jankae/battery-sim/pictures/IMG_2403.JPG

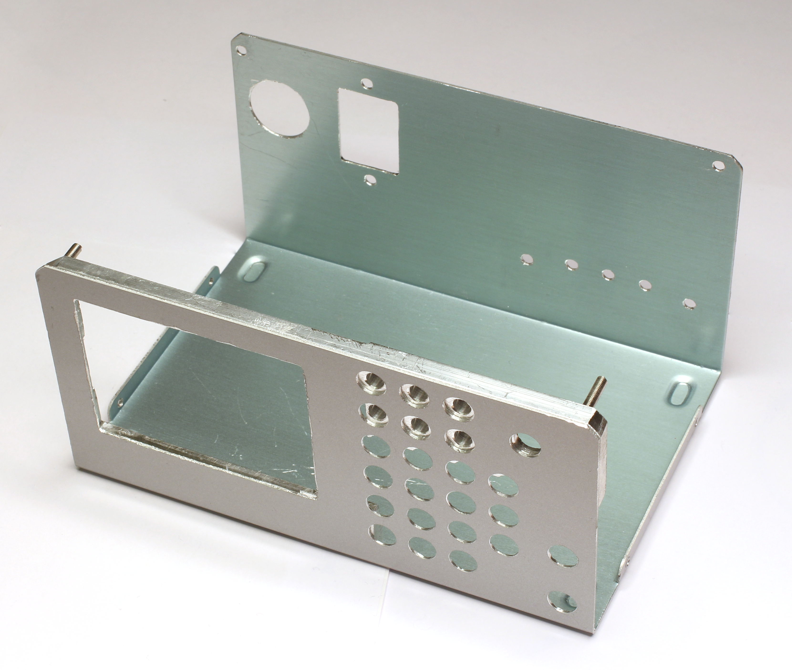
pictures/IMG_2403.JPG
