jankae/battery-sim/pictures/IMG_2404.JPG

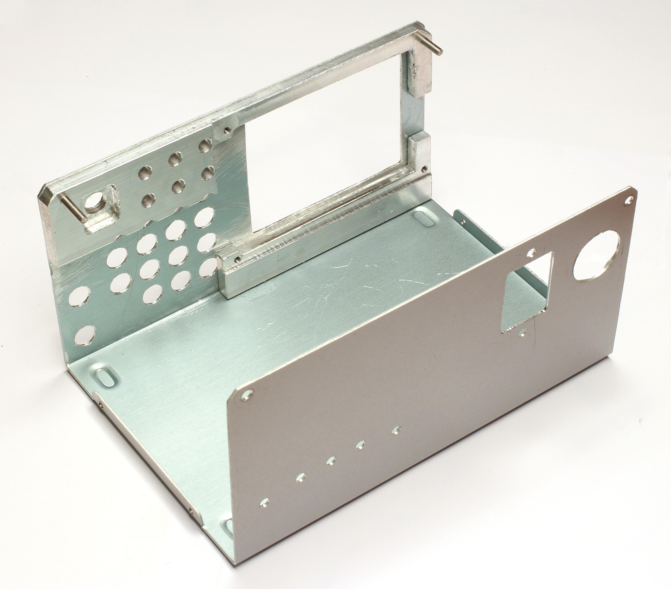
pictures/IMG_2404.JPG
