jankae/battery-sim/pictures/IMG_2405.JPG

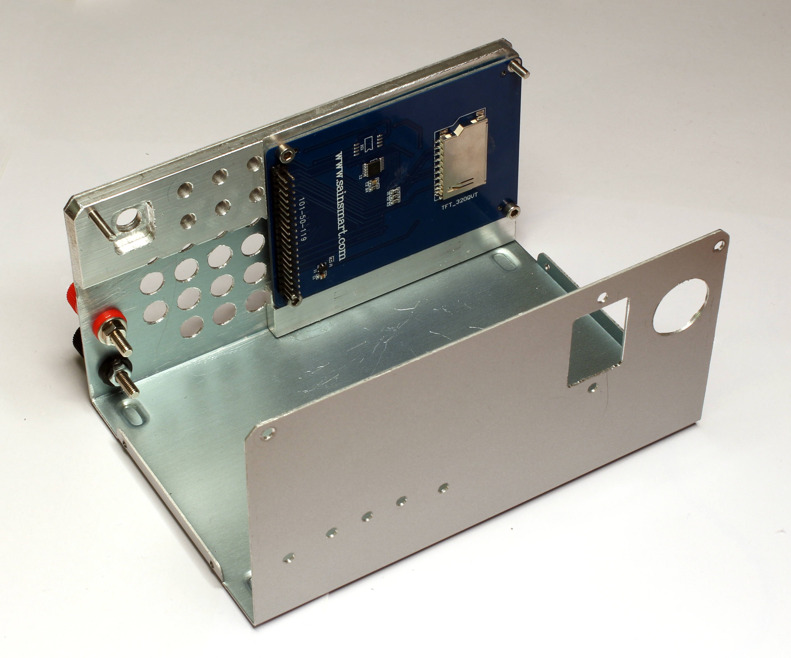
pictures/IMG_2405.JPG
