jankae/battery-sim/pictures/IMG_2406.JPG

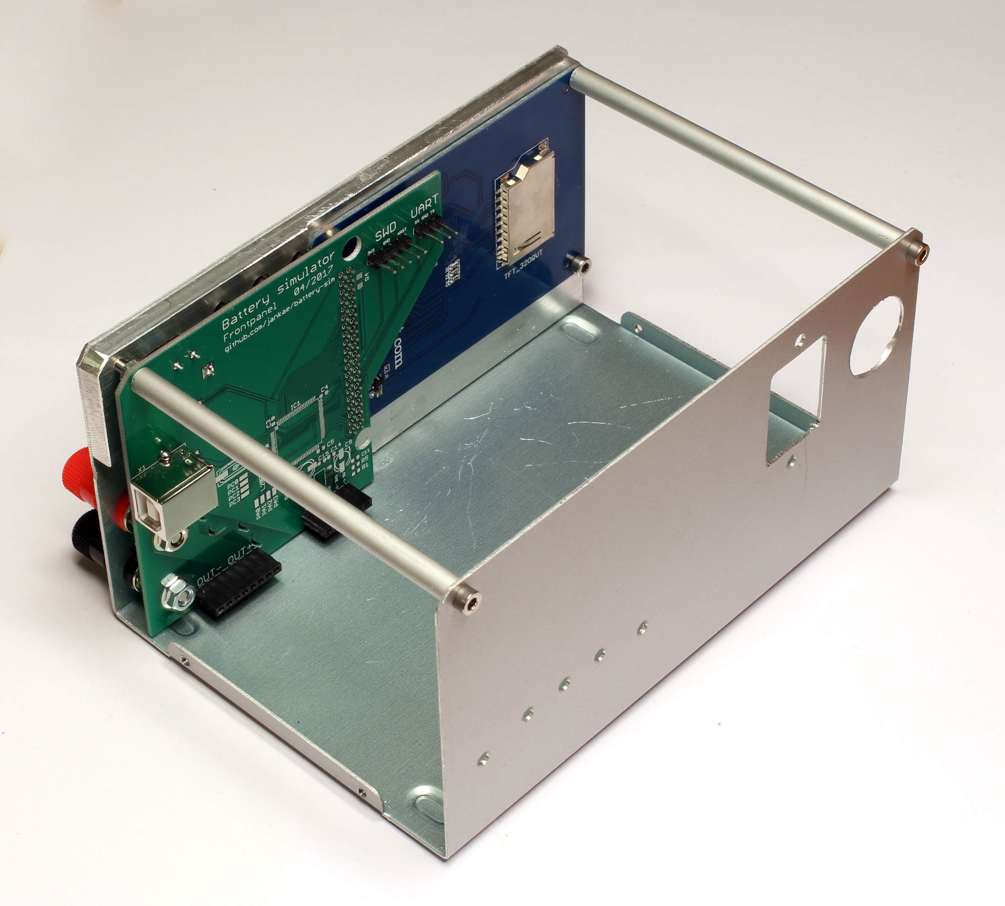
pictures/IMG_2406.JPG
