jankae/battery-sim/pictures/IMG_2407.JPG

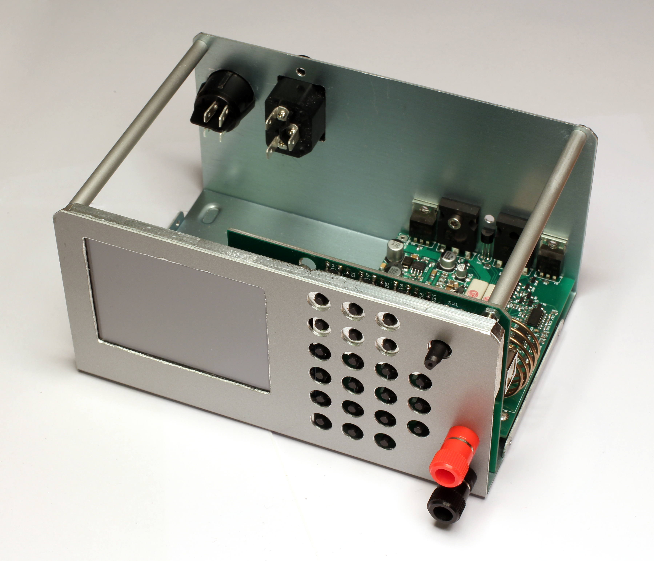
pictures/IMG_2407.JPG
