jankae/battery-sim/pictures/IMG_4996.JPG

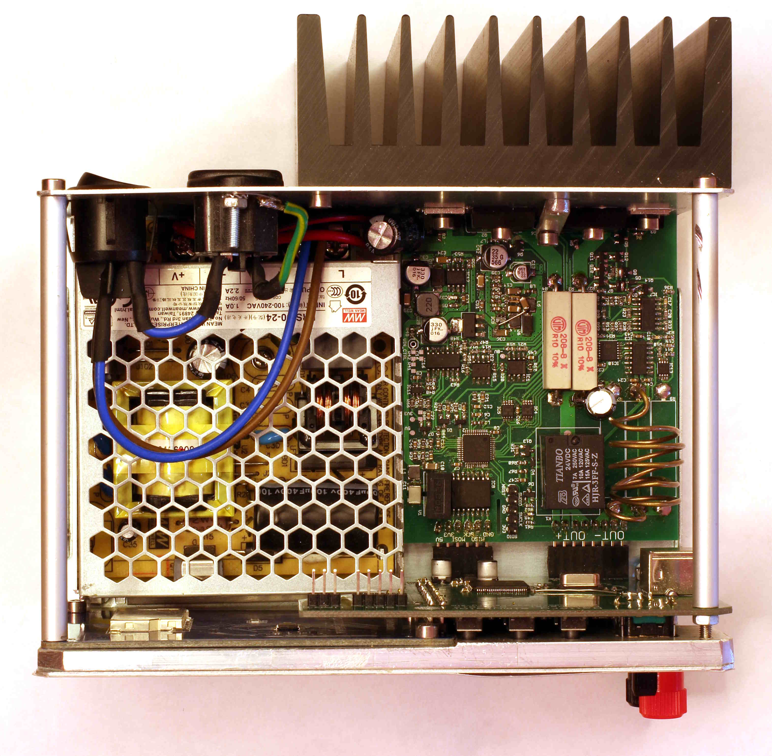
pictures/IMG_4996.JPG
