jankae/battery-sim/software/batsim/Abstraction/display.h

#ifndef DISPLAY_H_
#define DISPLAY_H_

#include "gpio.h"
#include "font.h"
#include "color.h"
#include "common.h"

#define DISPLAY_WIDTH		320
#define DISPLAY_HEIGHT		240

#ifdef __cplusplus
extern "C"
{
#endif

void display_Init(void);
void display_SetFont(font_t f);
void display_SetForeground(color_t c);
color_t display_GetForeground(void);
void display_SetBackground(color_t c);
color_t display_GetBackground(void);
void display_Clear();
void display_Pixel(uint16_t x, uint16_t y, uint16_t color);
void display_HorizontalLine(uint16_t x, uint16_t y, uint16_t length);
void display_VerticalLine(uint16_t x, uint16_t y, uint16_t length);
void display_Line(uint16_t x0, uint16_t y0, uint16_t x1, uint16_t y1);
void display_Rectangle(uint16_t x0, uint16_t y0, uint16_t x1, uint16_t y1);
void display_RectangleFull(uint16_t x0, uint16_t y0, uint16_t x1, uint16_t y1);
void display_Circle(uint16_t x0, uint16_t y0, uint16_t radius);
void display_CircleFull(uint16_t x0, uint16_t y0, uint16_t radius);
void display_Char(uint16_t x, uint16_t y, uint8_t c);
void display_String(uint16_t x, uint16_t y, const char *s);
void display_Image(uint16_t x, uint16_t y, const Image_t *im);
void display_ImageGrayscale(uint16_t x, uint16_t y, const Image_t *im);
void display_SetActiveArea(uint16_t minx, uint16_t maxx, uint16_t miny, uint16_t maxy);
void display_SetDefaultArea();

#ifdef __cplusplus
}
#endif

#endif
